oscgonfer/iron-skulls-mask/radio/bridge/patch.py

# Names dict
names = {
    'DIEGO': 10,
    'BUBA': 12,
    'MOE': 13,
    'LUIS': 14,
    'D': 10,
    'B': 12,
    'M': 13,
    'L': 14,
    'ALL': 99
}

'''
{
    State {
        Frequency band# : [list of channels]
    }
}
'''
channels_freq = {
    1: {
        1: [50, 59, 68, 77, 86, 95, 104, 113, 122],
        2: [30, 31, 32, 33, 34, 35]
    },
    2: {
        1: [59, 68, 77, 104, 113],
        2: [46, 45]
    },
    3: {
        1: [50, 59, 68, 77, 86, 95, 104, 113, 122],
        2: [46, 45]
    },
    4: {
        1: [68, 104, 113]
    },
    5: {
        1: [50, 59, 68, 77, 86, 95, 104, 113, 122],
        2: [30, 31, 32, 33, 34, 35]
    },
    6: {
        1: [50, 59, 68, 77, 86, 95, 104, 113, 122]
    },
}

'''
{
    State {
        Frequency band #: [min intensity, max intensity]
    }
}
'''
ranges_freq = {
    1: {
        1: [15, 30],
        2: [20, 50]
    },
    2: {
        1: [15, 30],
        2: [20, 50]
    },
    3: {
        1: [15, 30],
        2: [20, 50]
    },
    4: {
        1: [15, 30],
        2: [20, 50]
    },
    5: {
        1: [40, 100],
        2: [30, 100]
    },
    6: {
        1: [50, 100]
    },
}

personality = {
    'RED': 1,
    'GREEN': 2,
    'BLUE': 3,
    'WHITE': 4,
    'AMBER': 5,
    'INDIGO': 6,
    'STROBE': 7,
}

patch = {
	1: 92,
    2: 94,
    3: 88,
    7: 90,
    8: 95,
    9: 72,
    10: 82,
    11: 5,
    12: 16,
    13: 9,
    14: 20,
    15: 24,
    16: 96,
    17: 71,
    18: 169,
    19: 170,
    20: 227,
    21: 221,
    22: 50,
    23: 49,
    24: 51,
    25: 78,
    26: 93,
    27: 91,
    28: 90,
    29: 89,
    30: 164,
    31: 226,
    32: 224,
    33: 158,
    34: 220,
    35: 218,
    36: 163,
    37: 225,
    38: 223,
    39: 157,
    40: 219,
    41: 217,
    42: 166,
    43: 165,
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
}
